Kybernetika-SPSE/Hyncikova-RP/Ročníkovka/Zapojení/Kocici_krmic.kicad_sch

## KiCad design Ročníkovka/Zapojení/Kocici_krmic.kicad_sch (2026-04-29)

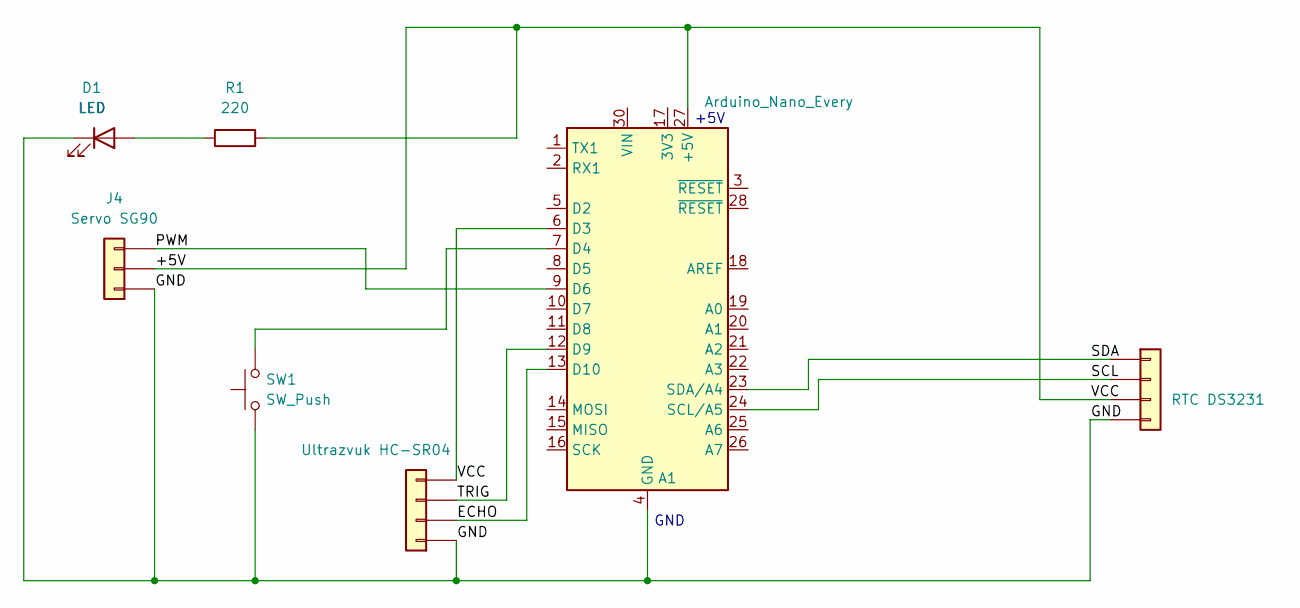
[picture p35: schematic Kocici_krmic.kicad_sch]

Parts:
A1: Arduino_Nano_Every; Arduino_Nano
D1: LED; LED_miniPLCC_2315_Handsoldering
J2: RTC DS3231
J3: Ultrazvuk HC-SR04
J4: Servo SG90
R1: 220; R_0201_0603Metric_Pad0.64x0.40mm_HandSolder
SW1: SW_Push

Connections:
+5V: A1.6 (D3), A1.27 (+5V), J2.3, J3.4, J4.2, R1.2
ECHO: A1.13 (D10), J3.2
GND: A1.4 (GND), A1.29 (GND), D1.1 (K), J2.4, J3.1, J4.1, SW1.1
unnamed: A1.7 (D4), SW1.2
unnamed: D1.2 (A), R1.1
PWM: A1.9 (D6), J4.3
SCL: A1.24 (SCL/A5), J2.2
SDA: A1.23 (SDA/A4), J2.1
TRIG: A1.12 (D9), J3.3

Notes on the sheet:
LED
+5V
GND
